UterGrooll/PLC_PRS10/screenshot/20251112_142928.jpg

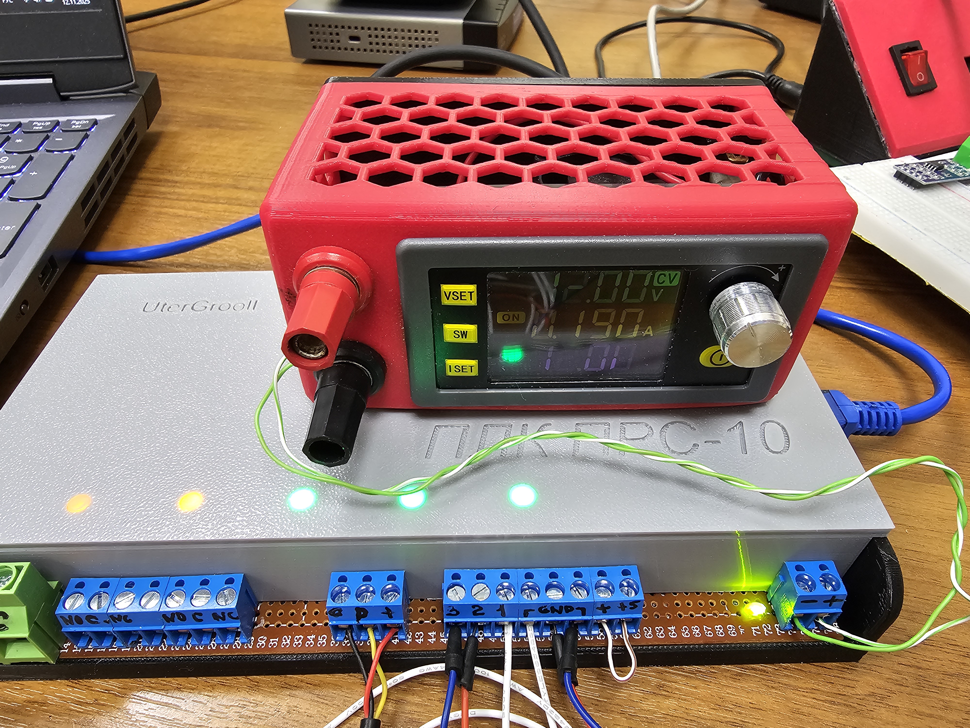
screenshot/20251112_142928.jpg
